eptecon/NoiseDetector/Firmware/components/bootwifi_app/main/BootWiFi.cpp

/**
 * Bootwifi - Boot the WiFi environment.
 *
 * Compile with -DBOOTWIFI_OVERRIDE_GPIO=<num> where <num> is a GPIO pin number
 * to use a GPIO override.
 * See the README.md for full information.
 *
 */
#include <freertos/FreeRTOS.h>
#include <freertos/task.h>
#include <esp_log.h>
#include <esp_err.h>
#include <nvs_flash.h>
#include <CPPNVS.h>
#include "driver/gpio.h"
//#include <tcpip_adapter.h>
//#include <lwip/sockets.h>
#include <WiFi.h>
#include <string.h>
#include <string>
#include <HttpServer.h>
#include <System.h>
#include <GeneralUtils.h>
#include "BootWiFi.h"
#include "sdkconfig.h"
#include "selectAP.h"

// If the structure of a record saved for a subsequent reboot changes
// then consider using semver to change the version number or else
// we may try and boot with the wrong data.
#define KEY_VERSION "version"
uint32_t g_version=0x0100;
gpio_config_t io_int_bootwifi;

#define KEY_CONNECTION_INFO "connectionInfo"   // Key used in NVS for connection info
#define BOOTWIFI_NAMESPACE  "bootwifi"         // Namespace in NVS for bootwifi
#define SSID_SIZE           (32)               // Maximum SSID size
#define PASSWORD_SIZE       (64)               // Maximum password size


/**
 * The information about a WiFi access point connection.
 */
typedef struct {
	char ssid[SSID_SIZE];
	char password[PASSWORD_SIZE];
	tcpip_adapter_ip_info_t ipInfo; // Optional static IP information
} connection_info_t;

//static bootwifi_callback_t g_callback = NULL; // Callback function to be invoked when we have finished.


// Forward declarations
static void saveConnectionInfo(connection_info_t *pConnectionInfo);

static const char LOG_TAG[] = "bootwifi";


static void dumpConnectionInfo(connection_info_t *pConnectionInfo) {
	ESP_LOGD(LOG_TAG, "connection_info.ssid = %.*s",     SSID_SIZE,     pConnectionInfo->ssid);
	ESP_LOGD(LOG_TAG, "connection_info.password = %.*s", PASSWORD_SIZE, pConnectionInfo->password);
	ESP_LOGD(LOG_TAG, "ip: %s, gw: %s, netmask: %s",
		GeneralUtils::ipToString((uint8_t*)&pConnectionInfo->ipInfo.ip).c_str(),
		GeneralUtils::ipToString((uint8_t*)&pConnectionInfo->ipInfo.gw).c_str(),
		GeneralUtils::ipToString((uint8_t*)&pConnectionInfo->ipInfo.netmask).c_str());
}


/**
 * Retrieve the connection info.  A rc==0 means ok.
 */
static int getConnectionInfo(connection_info_t *pConnectionInfo) {
	ESP_LOGD(LOG_TAG, ">> getConnectionInfo");
	size_t     size;
	uint32_t   version;

	NVS myNamespace(BOOTWIFI_NAMESPACE);
	myNamespace.get(KEY_VERSION, version);

	// Check the versions match
	if ((version & 0xff00) != (g_version & 0xff00)) {
		ESP_LOGD(LOG_TAG, "Incompatible versions ... current is %x, found is %x", version, g_version);
		return -1;
	}

	size = sizeof(connection_info_t);
	myNamespace.get(KEY_CONNECTION_INFO, (uint8_t*)pConnectionInfo, size);

	// Do a sanity check on the SSID
	if (strlen(pConnectionInfo->ssid) == 0) {
		ESP_LOGD(LOG_TAG, "NULL ssid detected");
		return -1;
	}
	dumpConnectionInfo(pConnectionInfo);
	ESP_LOGD(LOG_TAG, "<< getConnectionInfo");
	return 0;

} // getConnectionInfo


/**
 * Save our connection info for retrieval on a subsequent restart.
 */
static void saveConnectionInfo(connection_info_t *pConnectionInfo) {
	dumpConnectionInfo(pConnectionInfo);
	NVS myNamespace(BOOTWIFI_NAMESPACE);
	myNamespace.set(KEY_CONNECTION_INFO, (uint8_t*)pConnectionInfo, sizeof(connection_info_t));
	myNamespace.set(KEY_VERSION, g_version);
	myNamespace.commit();
} // setConnectionInfo


/**
 * Retrieve the signal level on the OVERRIDE_GPIO pin.  This is used to
 * indicate that we should not attempt to connect to any previously saved
 * access point we may know about.
 */

static int checkOverrideGpio() {
#ifdef BOOTWIFI_OVERRIDE_GPIO
	gpio_pad_select_gpio(BOOTWIFI_OVERRIDE_GPIO);
	gpio_set_direction(BOOTWIFI_OVERRIDE_GPIO, GPIO_MODE_INPUT);
	gpio_set_pull_mode(BOOTWIFI_OVERRIDE_GPIO, GPIO_PULLDOWN_ONLY);
	return gpio_get_level(BOOTWIFI_OVERRIDE_GPIO);
#else
	return 0; // If no boot override, return false
#endif
} // checkOverrideGpio

static void sendForm(HttpRequest* pRequest, HttpResponse* pResponse) {
  pResponse->setStatus(HttpResponse::HTTP_STATUS_OK, "OK");
  pResponse->addHeader(HttpRequest::HTTP_HEADER_CONTENT_TYPE, "text/html");
	pResponse->sendData(std::string((char*)selectAP_html, selectAP_html_len));
	pResponse->close();
} // sendForm


static void copyData(uint8_t* pTarget, size_t targetLength, std::string source) {
	memset(pTarget, 0, targetLength);
	size_t copySize = (source.length() > targetLength)? targetLength:source.length();
	memcpy(pTarget, source.data(), copySize);
	if (copySize < targetLength) {
		pTarget[copySize] = '\0';
	}
} // copyData


/**
 * @brief Process the form response.
 */
static void processForm(HttpRequest* pRequest, HttpResponse* pResponse) {
	ESP_LOGD(LOG_TAG, ">> processForm");
	std::map<std::string, std::string> formMap = pRequest->parseForm();
	connection_info_t connectionInfo;
	copyData((uint8_t*)connectionInfo.ssid, SSID_SIZE, formMap["ssid"]);
	copyData((uint8_t*)connectionInfo.password, PASSWORD_SIZE, formMap["password"]);

	try {
		std::string ipStr = formMap.at("ip");
		if (ipStr.empty()) {
			ESP_LOGD(LOG_TAG, "No IP address using default 0.0.0.0");
			connectionInfo.ipInfo.ip.addr = 0;
		} else {
			inet_pton(AF_INET, ipStr.c_str(), &connectionInfo.ipInfo.ip);
		}
	} catch(std::out_of_range& e) {
		ESP_LOGD(LOG_TAG, "No IP address using default 0.0.0.0");
		connectionInfo.ipInfo.ip.addr = 0;
	}

	try {
		std::string gwStr = formMap.at("gw");
		if (gwStr.empty()) {
			ESP_LOGD(LOG_TAG, "No GW address using default 0.0.0.0");
			connectionInfo.ipInfo.gw.addr = 0;
		} else {
			inet_pton(AF_INET, gwStr.c_str(), &connectionInfo.ipInfo.gw);
		}
	} catch(std::out_of_range& e) {
		ESP_LOGD(LOG_TAG, "No GW address using default 0.0.0.0");
		connectionInfo.ipInfo.gw.addr = 0;
	}

	try {
		std::string netmaskStr = formMap.at("netmask");
		if (netmaskStr.empty()) {
			ESP_LOGD(LOG_TAG, "No Netmask address using default 0.0.0.0");
			connectionInfo.ipInfo.netmask.addr = 0;
		} else {
			inet_pton(AF_INET, netmaskStr.c_str(), &connectionInfo.ipInfo.netmask);
		}
	} catch(std::out_of_range& e) {
		ESP_LOGD(LOG_TAG, "No Netmask address using default 0.0.0.0");
		connectionInfo.ipInfo.netmask.addr = 0;
	}

	ESP_LOGD(LOG_TAG, "ssid: %s, password: %s", connectionInfo.ssid, connectionInfo.password);

	saveConnectionInfo(&connectionInfo);

  pResponse->setStatus(HttpResponse::HTTP_STATUS_OK, "OK");
  pResponse->addHeader(HttpRequest::HTTP_HEADER_CONTENT_TYPE, "text/html");
	//pResponse->sendData(std::string((char*)selectAP_html, selectAP_html_len));
	pResponse->close();
	FreeRTOS::sleep(500);
	System::restart();
	ESP_LOGD(LOG_TAG, "<< processForm");
} // processForm


class BootWifiEventHandler: public WiFiEventHandler {
public:
	BootWifiEventHandler(BootWiFi *pBootWiFi) {
		m_pBootWiFi = pBootWiFi;
	}

	/**
	 * When the access point logic has started and we are able to receive incoming browser
	 * requests, start the internal HTTP Server.
	 */
	esp_err_t apStart() {
		ESP_LOGD("BootWifiEventHandler", ">> apStart");
		if (m_pBootWiFi->m_httpServerStarted == false) {
			m_pBootWiFi->m_httpServerStarted = true;
			m_pBootWiFi->m_httpServer.addPathHandler("GET",  "/",             sendForm);
			m_pBootWiFi->m_httpServer.addPathHandler("POST", "/ssidSelected", processForm);
			m_pBootWiFi->m_httpServer.start(80);
		}
		ESP_LOGD("BootWifiEventHandler", "<< apStart");
		return ESP_OK;
	} // apStaConnected

	/**
	 * If we fail to connect as a station, then become an access point and then
	 * become a web server.
	 */
	esp_err_t staDisconnected() {
		ESP_LOGD("BootWifiEventHandler", ">> staDisconnected");
		m_pBootWiFi->m_wifi.startAP("Duktape", "Duktape");
		ESP_LOGD("BootWifiEventHandler", "<< staDisconnected");
		return ESP_OK;
	} // staDisconnected


	esp_err_t staGotIp(system_event_sta_got_ip_t event_sta_got_ip) {
		ESP_LOGD("BootWifiEventHandler", ">> staGotIP");
		m_pBootWiFi->m_completeSemaphore.give();   // If we got an IP address, then we can end the boot process.
		ESP_LOGD("BootWifiEventHandler", "<< staGotIP");
		return ESP_OK;
	} // staGotIp

private:
	BootWiFi *m_pBootWiFi;
};


/**
 * Boot WiFi
 */
void BootWiFi::bootWiFi2() {
	ESP_LOGD(LOG_TAG, ">> bootWiFi2");

	// Check for a GPIO override which occurs when a physical Pin is high
	// during the test.  This can force the ability to check for new configuration
	// even if the existing configured access point is available.
	m_wifi.setWifiEventHandler(new BootWifiEventHandler(this));
	if (checkOverrideGpio()) {
		ESP_LOGD(LOG_TAG, "- GPIO override detected");
		m_wifi.startAP(m_ssid, m_password);
	} else {
		// There was NO GPIO override, proceed as normal.  This means we retrieve
		// our stored access point information of the access point we should connect
		// against.  If that information doesn't exist, then again we become an
		// access point ourselves in order to allow a client to connect and bring
		// up a browser.
		connection_info_t connectionInfo;
		int rc = getConnectionInfo(&connectionInfo);
		if (rc == 0) {
			// We have received connection information, let us now become a station
			// and attempt to connect to the access point.
			ESP_LOGD(LOG_TAG, "- Connecting to access point \"%s\" ...", connectionInfo.ssid);
			assert(strlen(connectionInfo.ssid) > 0);

		 	m_wifi.setIPInfo(
		 		connectionInfo.ipInfo.ip.addr,
		 		connectionInfo.ipInfo.gw.addr,
				connectionInfo.ipInfo.netmask.addr
			);
		  m_wifi.connectAP(connectionInfo.ssid, connectionInfo.password);   // Connect to the access point.

		} else {
			// We do NOT have connection information.  Let us now become an access
			// point that serves up a web server and allow a browser user to specify
			// the details that will be eventually used to allow us to connect
			// as a station.
			m_wifi.startAP(m_ssid, m_password);
		} // We do NOT have connection info
	}
	ESP_LOGD(LOG_TAG, "<< bootWiFi2");
} // bootWiFi2


/**
 * @brief Set the userid/password pair that will be used for the ESP32 access point.
 * @param [in] ssid The network id of the ESP32 when it becomes an access point.
 * @param [in] password The password for the ESP32 when it becomes an access point.
 */
void BootWiFi::setAccessPointCredentials(std::string ssid, std::string password) {
	m_ssid     = ssid;
	m_password = password;
} // setAccessPointCredentials



/**
 * @brief Main entry point into booting WiFi
 */
void BootWiFi::boot() {
	ESP_LOGD(LOG_TAG, ">> boot");
	ESP_LOGD(LOG_TAG, " +----------+");
	ESP_LOGD(LOG_TAG, " | BootWiFi |");
	ESP_LOGD(LOG_TAG, " +----------+");
	ESP_LOGD(LOG_TAG, " Access point credentials: %s/%s", m_ssid.c_str(), m_password.c_str());
	m_completeSemaphore.take("boot");     // Take the semaphore which will be unlocked when we complete booting.
	bootWiFi2();
	m_completeSemaphore.wait("boot");     // Wait for the semaphore that indicated we have completed booting.
	m_wifi.setWifiEventHandler(nullptr);  // Remove the WiFi boot handler when we have completed booting.
	ESP_LOGD(LOG_TAG, "<< boot");
} // boot

BootWiFi::BootWiFi() {
	m_httpServerStarted = false;
	setAccessPointCredentials("esp32", "password");   // Default access point credentials
}
